yasassb/self-balancing-monowheel-robot/Mechanical_Design/v4/ROCO_P12.SLDPRT

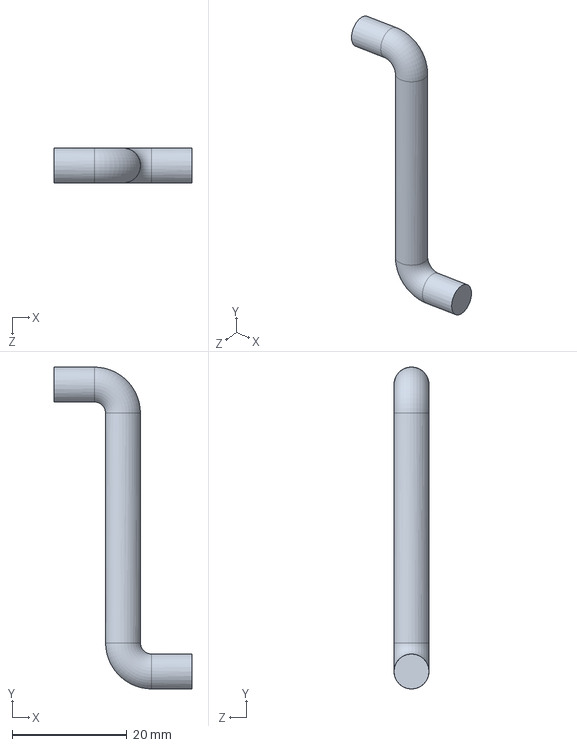
[picture p35: CAD file, 2025-05-31]
Mechanical_Design/v4/ROCO_P12.SLDPRT
24.0 x 56.1 x 6.10 mm
