yasassb/self-balancing-monowheel-robot/Mechanical_Design/v4/ROCO_P04.SLDPRT

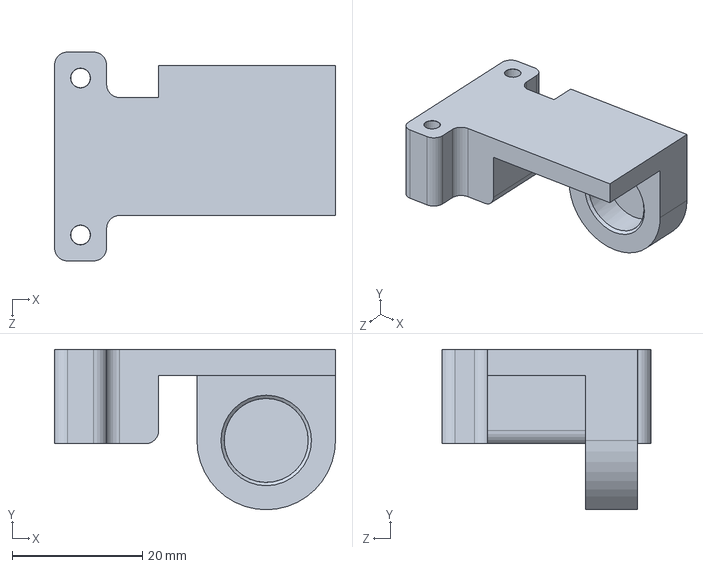
[picture p36: CAD file, 2025-05-31]
Mechanical_Design/v4/ROCO_P04.SLDPRT
43.2 x 24.6 x 32.1 mm
