yasassb/self-balancing-monowheel-robot/Mechanical_Design/v1/Bearing_Test.SLDPRT

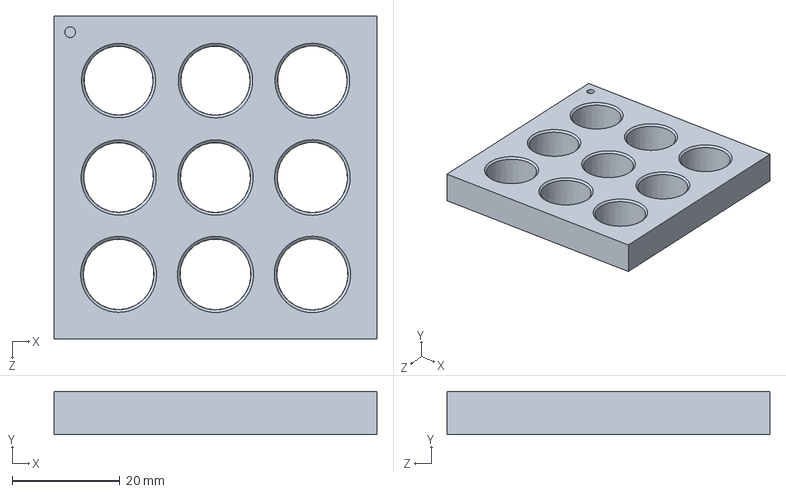
[picture p37: CAD file, 2025-05-31, an earlier design]
Mechanical_Design/v1/Bearing_Test.SLDPRT
60.0 x 8.00 x 60.0 mm
