yasassb/self-balancing-monowheel-robot/Controller_Algorithm/Combined_cpp/Camera_Ultrasonic/camera_index.h

//File: index_ov2640.html.gz, Size: 6787
#define index_ov2640_html_gz_len 6787
const uint8_t index_ov2640_html_gz[] = {
 0x1F, 0x8B, 0x08, 0x08, 0x23, 0xFC, 0x69, 0x5E, 0x00, 0x03, 0x69, 0x6E, 0x64, 0x65, 0x78, 0x5F,
 0x6F, 0x76, 0x32, 0x36, 0x34, 0x30, 0x2E, 0x68, 0x74, 0x6D, 0x6C, 0x00, 0xED, 0x3D, 0x6B, 0x73,
 0xDB, 0x46, 0x92, 0xDF, 0xFD, 0x2B, 0x60, 0x24, 0x6B, 0x92, 0x25, 0x92, 0x22, 0x29, 0x4A, 0x96,
 0x15, 0x89, 0x3E, 0x5B, 0x96, 0x1F, 0xB5, 0x76, 0xE2, 0xB5, 0x12, 0xC7, 0x5B, 0xA9, 0x2D, 0x07,
 0x04, 0x86, 0x24, 0x62, 0x10, 0xE0, 0x02, 0xA0, 0x48, 0x26, 0xA5, 0xDF, 0x71, 0x3F, 0xE8, 0xFE,
 0xD8, 0x75, 0xCF, 0x03, 0x18, 0x00, 0x83, 0x07, 0x49, 0x89, 0xF4, 0xFA, 0x8E, 0x4E, 0x45, 0x78,
 0x4C, 0xF7, 0xF4, 0xBB, 0x7B, 0x66, 0x30, 0xC0, 0xF9, 0x43, 0xCB, 0x33, 0xC3, 0xD5, 0x8C, 0x68,
 0x93, 0x70, 0xEA, 0x0C, 0x1E, 0x9C, 0xB3, 0x3F, 0x1A, 0xFC, 0xCE, 0x27, 0xC4, 0xB0, 0xD8, 0x21,
 0x3D, 0x9D, 0x92, 0xD0, 0xD0, 0xCC, 0x89, 0xE1, 0x07, 0x24, 0xBC, 0xD0, 0xE7, 0xE1, 0xA8, 0x75,
 0xAA, 0xA7, 0x6F, 0xBB, 0xC6, 0x94, 0x5C, 0xE8, 0x37, 0x36, 0x59, 0xCC, 0x3C, 0x3F, 0xD4, 0x35,
 0xD3, 0x73, 0x43, 0xE2, 0x42, 0xF3, 0x85, 0x6D, 0x85, 0x93, 0x0B, 0x8B, 0xDC, 0xD8, 0x26, 0x69,
 0xD1, 0x93, 0xA6, 0xED, 0xDA, 0xA1, 0x6D, 0x38, 0xAD, 0xC0, 0x34, 0x1C, 0x72, 0xD1, 0x95, 0x71,
 0x85, 0x76, 0xE8, 0x90, 0xC1, 0xD5, 0xF5, 0xFB, 0xA3, 0x9E, 0xF6, 0xD3, 0xC7, 0x5E, 0xFF, 0xA4,
 0x73, 0x7E, 0xC8, 0xAE, 0xC5, 0x6D, 0x82, 0x70, 0x25, 0x9F, 0xE3, 0x6F, 0xE8, 0x59, 0x2B, 0xED,
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
 0x8F, 0xB5, 0x86, 0xE3, 0x9A, 0xE0, 0x08, 0x06, 0x0D, 0x37, 0x16, 0x5C, 0x81, 0x81, 0x63, 0x41,
 0xF6, 0x24, 0x2C, 0x67, 0xF8, 0x8C, 0x28, 0x11, 0xB9, 0xDB, 0xE0, 0x4F, 0x21, 0xE4, 0xE0, 0x2F,
 0xD7, 0x81, 0x24, 0x3C, 0x52, 0xF4, 0x59, 0xFA, 0x12, 0x29, 0x4C, 0xD3, 0x19, 0xFE, 0xE6, 0xC6,
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
};
