yasassb/self-balancing-monowheel-robot/Controller_Algorithm/Combined_cpp/Camera_Ultrasonic/Usnic.ino

// Ultrasonic Sensor Pins
const int trigPin = D5;
const int echoPin = D6;

// Global Variables
#define SOUND_VELOCITY 0.034
#define CM_TO_INCH 0.393701

unsigned long previousMillis = 0;
float dist_thresh = 25;

unsigned long pundtim;

void usnic_init() {

  pinMode(trigPin, OUTPUT);
  pinMode(echoPin, INPUT);
}

bool measureDistance() {

  // Clear the trigPin
  digitalWrite(trigPin, LOW);
  delayMicroseconds(2);

  // Trigger pulse
  digitalWrite(trigPin, HIGH);
  delayMicroseconds(10);
  digitalWrite(trigPin, LOW);

  // Measure pulse duration
  long duration = pulseIn(echoPin, HIGH);

  // Validate measurement
  if (duration > 0) {
    distanceCm = duration * SOUND_VELOCITY / 2;

    if (distanceCm > 400) return false;
    else if (distanceCm < dist_thresh) {

      if (!ovr) {

        out_send(0, 0);
        ovr = true;
        pundtim = millis();
      }
    } else if (distanceCm >= dist_thresh) {

      if ((millis() - pundtim) >= 6000) {

        out_send(1, 0);
        ovr = false;
      }
    }

    // Log distance
    // Serial.print("Distance (cm): ");
    // Serial.println(distanceCm);

    return true;
  }

  return false;
}
